scientiaetlabor/ae-smart-shunt/firmware/src/espnow_handler.cpp

#include "espnow_handler.h"
#include "esp_err.h"
#include <cstring>

// 🔒 Compile-time check: catch padding/alignment mismatches.
// Update "EXPECTED_AE_SMART_SHUNT_STRUCT_SIZE" if your struct changes.
#define EXPECTED_AE_SMART_SHUNT_STRUCT_SIZE 69   // <-- adjust to your intended size
static_assert(sizeof(struct_message_ae_smart_shunt_1) == EXPECTED_AE_SMART_SHUNT_STRUCT_SIZE,
              "struct_message_ae_smart_shunt_1 has unexpected size! Possible padding/alignment issue.");

ESPNowHandler::ESPNowHandler(const uint8_t *broadcastAddr)
{
    memcpy(broadcastAddress, broadcastAddr, 6);
    memset(&peerInfo, 0, sizeof(peerInfo));
    // Optionally zero the local struct
    memset(&localAeSmartShuntStruct, 0, sizeof(localAeSmartShuntStruct));
}

void ESPNowHandler::setAeSmartShuntStruct(const struct_message_ae_smart_shunt_1 &shuntStruct)
{
    // shallow copy of struct (same layout). If you need cross-platform compatibility,
    // serialize the fields into a packed buffer instead.
    localAeSmartShuntStruct = shuntStruct;
}

void ESPNowHandler::printMacAddress(const uint8_t* mac) {
    char buf[32];
    snprintf(buf, sizeof(buf), "%02X:%02X:%02X:%02X:%02X:%02X",
             mac[0], mac[1], mac[2], mac[3], mac[4], mac[5]);
    Serial.println(buf);
}

void ESPNowHandler::sendMessageAeSmartShunt()
{
    uint8_t *data = (uint8_t *)&localAeSmartShuntStruct;
    size_t len = sizeof(localAeSmartShuntStruct);

    Serial.printf("Struct size: %d bytes\n", len);

    Serial.print("Sending to MAC: ");
    printMacAddress(broadcastAddress);

    // Serial.print("Sending data (hex): ");
    // for (size_t i = 0; i < len; i++)
    // {
    //     Serial.printf("%02X ", data[i]);
    // }

    // Serial.print(" | ASCII: ");
    // for (size_t i = 0; i < len; i++)
    // {
    //     char c = data[i];
    //     Serial.print(isprint(c) ? c : '.');
    // }
    Serial.println();

    esp_err_t result = esp_now_send(broadcastAddress, data, len);
    if (result == ESP_OK)
    {
        Serial.println("Sent AE Smart Shunt message successfully");
    }
    else
    {
        Serial.print("Error sending AeSmartShunt data: ");
        Serial.println(esp_err_to_name(result));
    }
}

bool ESPNowHandler::begin()
{
    WiFi.mode(WIFI_MODE_STA);
    // Disable WiFi scan power save if needed (optional).
    if (esp_now_init() != ESP_OK)
    {
        Serial.println("Error initializing ESP-NOW");
        return false;
    }
    return true;
}

void ESPNowHandler::registerSendCallback(esp_now_send_cb_t callback)
{
    esp_now_register_send_cb(callback);
}

bool ESPNowHandler::addPeer()
{
    memset(&peerInfo, 0, sizeof(peerInfo));
    memcpy(peerInfo.peer_addr, broadcastAddress, 6);
    peerInfo.channel = 0; // 0 means current WiFi channel. Set explicitly if needed.
    peerInfo.encrypt = false;

    if (esp_now_add_peer(&peerInfo) != ESP_OK)
    {
        Serial.println("Failed to add peer");
        return false;
    }
    return true;
}
